primesteam/EcoSeed/photos/photo4.jpg

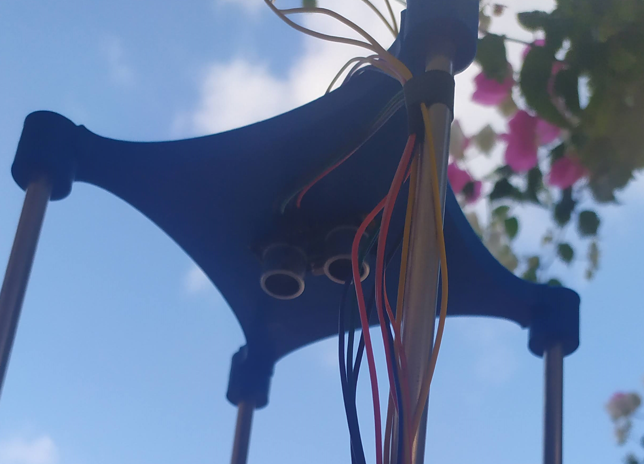
photos/photo4.jpg
