primesteam/EcoSeed/src/ultrasonic.ino

String get_distance() {
  // Write Ultrasonic Sensor Pins
  digitalWrite(trigPin, LOW);
  delayMicroseconds(2);
  digitalWrite(trigPin, HIGH);
  delayMicroseconds(10);
  digitalWrite(trigPin, LOW);

  // Measure Sensor Values
  long duration = pulseIn(echoPin, HIGH);
  float distanceCm = duration * SOUND_SPEED / 2;
  return String(distanceCm);
}
